No0ne/ps2x2pico/ps2kb.c

/*
 * The MIT License (MIT)
 *
 * Copyright (c) 2022 No0ne (https://github.com/No0ne)
 *           (c) 2023 Dustin Hoffman
 *
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
 */

#include "ps2phy.h"
ps2phy kb_phy;

u8 const led2ps2[] = { 0, 4, 1, 5, 2, 6, 3, 7 };
u8 const mod2ps2[] = { 0x14, 0x12, 0x11, 0x1f, 0x14, 0x59, 0x11, 0x27 };
u8 const hid2ps2[] = {
  0x00, 0x00, 0xfc, 0x00, 0x1c, 0x32, 0x21, 0x23, 0x24, 0x2b, 0x34, 0x33, 0x43, 0x3b, 0x42, 0x4b,
  0x3a, 0x31, 0x44, 0x4d, 0x15, 0x2d, 0x1b, 0x2c, 0x3c, 0x2a, 0x1d, 0x22, 0x35, 0x1a, 0x16, 0x1e,
  0x26, 0x25, 0x2e, 0x36, 0x3d, 0x3e, 0x46, 0x45, 0x5a, 0x76, 0x66, 0x0d, 0x29, 0x4e, 0x55, 0x54,
  0x5b, 0x5d, 0x5d, 0x4c, 0x52, 0x0e, 0x41, 0x49, 0x4a, 0x58, 0x05, 0x06, 0x04, 0x0c, 0x03, 0x0b,
  0x83, 0x0a, 0x01, 0x09, 0x78, 0x07, 0x7c, 0x7e, 0x7e, 0x70, 0x6c, 0x7d, 0x71, 0x69, 0x7a, 0x74,
  0x6b, 0x72, 0x75, 0x77, 0x4a, 0x7c, 0x7b, 0x79, 0x5a, 0x69, 0x72, 0x7a, 0x6b, 0x73, 0x74, 0x6c,
  0x75, 0x7d, 0x70, 0x71, 0x61, 0x2f, 0x37, 0x0f, 0x08, 0x10, 0x18, 0x20, 0x28, 0x30, 0x38, 0x40,
  0x48, 0x50, 0x57, 0x5f
};
u32 const repeats[] = {
  33333, 37453, 41667, 45872, 48309, 54054, 58480, 62500,
  66667, 75188, 83333, 91743, 100000, 108696, 116279, 125000,
  133333, 149254, 166667, 181818, 200000, 217391, 232558, 250000,
  270270, 303030, 333333, 370370, 400000, 434783, 476190, 500000
};
u16 const delays[] = { 250, 500, 750, 1000 };

bool kb_enabled = true;

bool blinking = false;
bool repeating = false;
u32 repeat_us;
u16 delay_ms;
alarm_id_t repeater;

u8 prev_rpt[] = { 0, 0, 0, 0, 0, 0, 0, 0 };
u8 repeat = 0;

void kb_send(u8 byte) {
  queue_try_add(&kb_phy.qbytes, &byte);
}

void kb_maybe_send_e0(u8 byte) {
  if(byte == 0x46 ||
    (byte >= 0x49 && byte <= 0x52) ||
     byte == 0x54 || byte == 0x58 ||
     byte == 0x65 || byte == 0x66 ||
    (byte >= 0x81 && byte < 0xe0) ||
    (byte > 0xe2 && byte != 0xe5)) {
    kb_send(0xe0);
  }
}

void kb_set_leds(u8 byte) {
  if(byte > 7) byte = 0;
  tuh_kb_set_leds(led2ps2[byte]);
}

int64_t blink_callback() {
  if(blinking) {
    kb_set_leds(7);
    blinking = false;
    return 500000;
  }
  
  //if(kb_addr) {
  kb_set_leds(0);
  kb_send(0xaa);
  //} else {
  //  kb_send(0xfc);
  //}
  
  return 0;
}

void kb_reset() {
  kb_enabled = true;
  repeat_us = 91743;
  delay_ms = 500;
  repeat = 0;
  blinking = true;
  add_alarm_in_ms(1, blink_callback, NULL, false);
}

int64_t repeat_callback() {
  if(repeat) {
    repeating = true;
    return repeat_us;
  }
  
  repeater = 0;
  return 0;
}

void kb_send_key(u8 key, bool state, u8 modifiers) {
  if(!kb_enabled) return;
  if(key >= sizeof(hid2ps2) && key < 0xe0 && key > 0xe7) return;
  
  if(key == 0x48) {
    repeat = 0;
    
    if(state) {
      if(modifiers & 0x1 || modifiers & 0x10) {
        kb_send(0xe0); kb_send(0x7e); kb_send(0xe0); kb_send(0xf0); kb_send(0x7e);
      } else {
        kb_send(0xe1); kb_send(0x14); kb_send(0x77); kb_send(0xe1);
        kb_send(0xf0); kb_send(0x14); kb_send(0xf0); kb_send(0x77);
      }
    }
    
    return;
  }
  
  kb_maybe_send_e0(key);
  
  if(state) {
    repeat = key;
    if(repeater) cancel_alarm(repeater);
    repeater = add_alarm_in_ms(delay_ms, repeat_callback, NULL, false);
  } else {
    if(key == repeat) repeat = 0;
    kb_send(0xf0);
  }
  
  if(key >= 0xe0 && key <= 0xe7) {
    kb_send(mod2ps2[key - 0xe0]);
  } else {
    kb_send(hid2ps2[key]);
  }
}

void kb_usb_receive(u8 const* report) {
  if(report[1] == 0) {
  
    if(report[0] != prev_rpt[0]) {
      u8 rbits = report[0];
      u8 pbits = prev_rpt[0];
      
      for(u8 j = 0; j < 8; j++) {
        if((rbits & 0x1) != (pbits & 0x1)) {
          kb_send_key(j + 0xe0, rbits & 0x1, report[0]);
        }
        
        rbits = rbits >> 1;
        pbits = pbits >> 1;
      }
    }
    
    for(u8 i = 2; i < 8; i++) {
      if(prev_rpt[i]) {
        bool brk = true;
        
        for(u8 j = 2; j < 8; j++) {
          if(prev_rpt[i] == report[j]) {
            brk = false;
            break;
          }
        }
        
        if(brk) {
          kb_send_key(prev_rpt[i], false, report[0]);
        }
      }
      
      if(report[i]) {
        bool make = true;
        
        for(u8 j = 2; j < 8; j++) {
          if(report[i] == prev_rpt[j]) {
            make = false;
            break;
          }
        }
        
        if(make) {
          kb_send_key(report[i], true, report[0]);
        }
      }
    }
    
    memcpy(prev_rpt, report, sizeof(prev_rpt));
  }
}

void kb_receive(u8 byte, u8 prev_byte) {
  switch (prev_byte) {
    case 0xed: // Set LEDs
      kb_set_leds(byte);
    break;
    
    case 0xf3: // Set typematic rate and delay
      repeat_us = repeats[byte & 0x1f];
      delay_ms = delays[(byte & 0x60) >> 5];
    break;
    
    default:
      switch (byte) {
        case 0xff: // Reset
          kb_reset();
        break;
        
        case 0xee: // Echo
          kb_send(0xee);
        return;
        
        case 0xf2: // Identify keyboard
          kb_send(0xfa);
          kb_send(0xab);
          kb_send(0x83);
        return;
        
        case 0xf4: // Enable scanning
          kb_enabled = true;
        break;
        
        case 0xf5: // Disable scanning, restore default parameters
        case 0xf6: // Set default parameters
          kb_enabled = byte == 0xf6;
          repeat_us = 91743;
          delay_ms = 500;
          repeat = 0;
          kb_set_leds(0);
        break;
      }
    break;
  }
  
  kb_send(0xfa);
}

bool kb_task() {
  ps2phy_task(&kb_phy);
  
  if(repeating) {
    repeating = false;
    
    if(repeat) {
      kb_maybe_send_e0(repeat);
      if(repeat >= 0xe0 && repeat <= 0xe7) {
        kb_send(mod2ps2[repeat - 0xe0]);
      } else {
        kb_send(hid2ps2[repeat]);
      }
    }
  }
  
  return kb_enabled && !kb_phy.busy;
}

void kb_init(u8 gpio) {
  ps2phy_init(&kb_phy, pio0, gpio, &kb_receive);
  kb_reset();
}
