No0ne/ps2x2pico/src/ps2ms.c

/*
 * The MIT License (MIT)
 *
 * Copyright (c) 2024 No0ne (https://github.com/No0ne)
 *           (c) 2023 Dustin Hoffman
 *
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
 */
#include "ps2x2pico.h"

ps2out ms_out;
ps2in ms_in;

#ifndef MS_RATE_DEFAULT
  #define MS_RATE_HOST_CONTROL
  #define MS_RATE_DEFAULT 100
#endif

bool ms_streaming = false;
bool ms_ismoving = false;
u32 ms_magic_seq = 0;
u8 ms_type = 0;
u8 ms_rate = MS_RATE_DEFAULT;
u8 ms_db = 0;
s16 ms_dx = 0;
s16 ms_dy = 0;
s8 ms_dz = 0;

void ms_reset() {
  ms_ismoving = false;
  ms_db = 0;
  ms_dx = 0;
  ms_dy = 0;
  ms_dz = 0;
}

void ms_send(u8 byte) {
  if(!ms_streaming) printf("ms > host %02x\n", byte);
  queue_try_add(&ms_out.qbytes, &byte);
}

s64 ms_reset_callback() {
  ms_send(0xaa);
  ms_send(ms_type);
  #ifdef MSIN
    ps2in_reset(&ms_in);
  #endif
  return 0;
}

u8 ms_clamp_xyz(s16 xyz) {
  if(xyz < -255) return 1;
  if(xyz > 255) return 255;
  return xyz;
}

s16 ms_remain_xyz(s16 xyz) {
  if(xyz < -255) return xyz + 255;
  if(xyz > 255) return xyz - 255;
  return 0;
}

s64 ms_send_callback() {
  if(!ms_streaming) return 0;

  if(!ms_out.busy) {
    if(!ms_db && !ms_dx && !ms_dy && !ms_dz) {
      if(!ms_ismoving) {
        return 1000000 / ms_rate;
      }

      ms_ismoving = false;
    } else {
      ms_ismoving = true;
    }

    u8 byte1 = 0x08 | (ms_db & 0x07);
    u8 byte2 = ms_clamp_xyz(ms_dx);
    u8 byte3 = 0x100 - ms_clamp_xyz(ms_dy);
    s8 byte4 = 0x100 - ms_dz;

    if(ms_dx < 0) byte1 |= 0x10;
    if(ms_dy > 0) byte1 |= 0x20;
    if(byte2 == 0xaa) byte2 = 0xab;
    if(byte3 == 0xaa) byte3 = 0xab;

    ms_send(byte1);
    ms_send(byte2);
    ms_send(byte3);

    if(ms_type == 3 || ms_type == 4) {
      if(byte4 < -8) byte4 = -8;
      if(byte4 > 7) byte4 = 7;

      if(ms_type == 4) {
        byte4 &= 0x0f;
        byte4 |= (ms_db << 1) & 0x30;
      }

      ms_send(byte4);
    }

    ms_dx = ms_remain_xyz(ms_dx);
    ms_dy = ms_remain_xyz(ms_dy);
    ms_dz = 0;
  }

  return 1000000 / ms_rate;
}

void ms_send_movement(u8 buttons, s8 x, s8 y, s8 z) {
  ms_db = buttons;
  ms_dx += x;
  ms_dy += y;
  ms_dz += z;
}

void ms_receive(u8 byte, u8 prev_byte) {
  printf("host > ms %02x\n", byte);
  switch (prev_byte) {
    case 0xf3: // Set Sample Rate
      #ifdef MS_RATE_HOST_CONTROL
        ms_rate = byte;
      #endif

      ms_magic_seq = ((ms_magic_seq << 8) | byte) & 0xffffff;

      if(ms_type == 0 && ms_magic_seq == 0xc86450) {
        ms_type = 3;
      } else if(ms_type == 3 && ms_magic_seq == 0xc8c850) {
        ms_type = 4;
      }

      ms_reset();
    break;

    default:
      switch(byte) {
        case 0xff: // Reset
          add_alarm_in_ms(100, ms_reset_callback, NULL, false);
          ms_type = 0;
          // fall through
        case 0xf6: // Set Defaults
          ms_rate = MS_RATE_DEFAULT;
          // fall through
        case 0xf5: // Disable Data Reporting
          ms_streaming = false;
          ms_reset();
        break;

        case 0xf4: // Enable Data Reporting
          ms_streaming = true;
          ms_reset();
          add_alarm_in_ms(100, ms_send_callback, NULL, false);
        break;

        case 0xf2: // Get Device ID
          ms_send(0xfa);
          ms_send(ms_type);
          ms_reset();
        return;

        case 0xeb: // Read Data
          ms_ismoving = true;
        break;
        
        case 0xe9: // Status Request
          ms_send(0xfa);
          ms_send(ms_streaming << 5); // Bit6: Mode, Bit 5: Enable, Bit 4: Scaling, Bits[2,1,0] = Buttons[L,M,R]
          ms_send(0x02); // Resolution
          ms_send(ms_rate); // Sample Rate
        return;
        
        default:
          ms_reset();
        break;
      }
    break;
  }
  
  ms_send(0xfa);
}

bool ms_task() {
  ps2out_task(&ms_out);
  #ifdef MSIN
    ps2in_task(&ms_in, &ms_out);
  #endif
  return ms_streaming && !ms_out.busy;
}

void ms_init(u8 gpio_out, u8 gpio_in) {
  ps2out_init(&ms_out, pio1, gpio_out, &ms_receive);
  #ifdef MSIN
    ps2in_init(&ms_in, pio0, gpio_in);
  #else
    (void)gpio_in;
  #endif
  ms_reset_callback();
}
